alexbegoon/meshimi/software/flipper/demo/meshimi_types.h

#pragma once

typedef enum {
    MeshimiViewIdMenu,
    MeshimiViewIdPopup,
    MeshimiViewIdTextInput,
    MeshimiViewIdWidget,
    MeshimiViewIdVariableItemList,
    MeshimiViewIdMode,
} MeshimiViewId;
